medicionco2/proyecto_medidor_co2/src/mhz19/ESP32/basic/secrets.h

/*

  secrets.h - Use this file to store the private credentials 
         and connection details

*/

#define SECRET_SSID "MySSID"      // replace MySSID with your WiFi network name
#define SECRET_PASS "MyPassword"  // replace MyPassword with your WiFi password
